3pnguyen/esp32-bluetooth-media-keyboard/Code/Finalized Code/include/functions.h

#pragma once

#include <Arduino.h>
#include <BleCombo.h>
#include <driver/gpio.h>
#include <esp_sleep.h>
#include "constants/pins.h"
#include "classes/IntervalTimer.h" 

void wakeUp();
void goToSleep();
void setIndicatorLedOff(int ledPin);
void setIndicatorLedsOff();
void setIndicatorLedHold(bool enabled);
void pressMediaKey(const uint8_t *key, String keyName = "", int debounce = 200);
int voltageToPercent(float v);
void blinkLED(int ledPin, int brightness, int cycles, int delayMs);
