3pnguyen/esp32-bluetooth-media-keyboard/Code/Finalized Code/src/functions.cpp

#include "functions.h"
#include "constants/led.h"

void wakeUp() {
    setIndicatorLedHold(false);
    setIndicatorLedsOff();
    null_reconnection.reset();
    delay(20);
    Keyboard.begin();
    setIndicatorLedsOff();
}

void goToSleep() {
    Serial.println("Entering sleep…");
    Serial.flush();
    setIndicatorLedsOff();
    Keyboard.end();
    setIndicatorLedsOff();
    setIndicatorLedHold(true);
    gpio_wakeup_enable((gpio_num_t)SLEEP_BUTTON, GPIO_INTR_HIGH_LEVEL);
    esp_sleep_enable_gpio_wakeup();
    esp_light_sleep_start();
    setIndicatorLedHold(false);
    setIndicatorLedsOff();
    gpio_wakeup_disable((gpio_num_t)SLEEP_BUTTON);
}

void setIndicatorLedOff(int ledPin) {
    analogWrite(ledPin, 0);
}

void setIndicatorLedsOff() {
    setIndicatorLedOff(INDICATOR_LED_R);
    setIndicatorLedOff(INDICATOR_LED_G);
    setIndicatorLedOff(INDICATOR_LED_B);
}

void setIndicatorLedHold(bool enabled) {
    if (enabled) {
        gpio_hold_en((gpio_num_t)INDICATOR_LED_R);
        gpio_hold_en((gpio_num_t)INDICATOR_LED_G);
        gpio_hold_en((gpio_num_t)INDICATOR_LED_B);
    } else {
        gpio_hold_dis((gpio_num_t)INDICATOR_LED_R);
        gpio_hold_dis((gpio_num_t)INDICATOR_LED_G);
        gpio_hold_dis((gpio_num_t)INDICATOR_LED_B);
    }
}

void pressMediaKey(const uint8_t *key, String keyName, int debounce) {
    if (keyName != "") Serial.println("→ " + keyName);
    Keyboard.write(key);

    analogWrite(INDICATOR_LED_R, R_BRIGHTNESS);
    analogWrite(INDICATOR_LED_G, G_BRIGHTNESS);
    analogWrite(INDICATOR_LED_B, B_BRIGHTNESS);

    delay(debounce);

    setIndicatorLedsOff();
}

int voltageToPercent(float v) {
    const int N = 9;
    const float volts[N] = {4.20, 4.00, 3.95, 3.90, 3.85, 3.80, 3.70, 3.60, 3.30};
    const int pct[N]   = {100,  85,   75,   60,   50,   35,   20,   10,    0};

    if (v >= volts[0]) return 100;
    if (v <= volts[N-1]) return 0;

    for (int i = 0; i < N-1; ++i) {
        if (v <= volts[i] && v >= volts[i+1]) {
        float t = (v - volts[i+1]) / (volts[i] - volts[i+1]); // 0..1
        float p = pct[i+1] + t * (pct[i] - pct[i+1]);
        return (int)round(p);
        }
    }
    return 0;
}

void blinkLED(int ledPin, int brightness, int cycles, int delayMs) {
    for (int i = 0; i < cycles; i++) {
        analogWrite(ledPin, brightness);
        delay(delayMs);
        setIndicatorLedOff(ledPin);
        delay(delayMs);
    }
}
