3pnguyen/esp32-bluetooth-media-keyboard/Code/Finalized Code/include/pins.h

#ifndef PINS_H
#define PINS_H

#define BUTTON_1 10 //D10
#define BUTTON_2 9 //D9
#define BUTTON_3 8 //D8
#define BUTTON_4 20 //D7
#define SLEEP_BUTTON 5 //D3
#define INDICATOR_LED_R 2 //D0
#define INDICATOR_LED_G 3 //D1
#define INDICATOR_LED_B 6 //D4
#define POWER_VD 4 //D2

#endif
