3pnguyen/esp32-bluetooth-media-keyboard/Code/Finalized Code/src/Incremental.cpp

#include "Incremental.h"

Incremental::Incremental(int start) : counter(start) {}

void Incremental::increment(int addend) {counter += addend;}

void Incremental::reset(int new_value) {counter = new_value;}
