3pnguyen/esp32-bluetooth-media-keyboard/Code/Finalized Code/include/ChangeDetector.h

#ifndef CHANGEDETECTOR_H
#define CHANGEDETECTOR_H

template <typename T>
class ChangeDetector {
  private:
    T previous;
    T current;

  public:
      ChangeDetector(T initial);
      bool update(T newValue);
      T get() const;
      void reset(T value);
};

#endif
