3pnguyen/esp32-bluetooth-media-keyboard/Code/Finalized Code/include/IntervalTimer.h

#ifndef INTERVALTIMER_H
#define INTERVALTIMER_H

class IntervalTimer {
  private:
    unsigned long lastTime = 0;
    unsigned long interval;

  public:
    IntervalTimer(unsigned long intervalMs);
    bool isReady();
    void reset();
};

#endif
